saneamentoambiental/SensorUmidade/src/CustomHtmlFormatProvider.h

#ifndef _CustomHtmlFormatProvider_H_
#define _CustomHtmlFormatProvider_H_

#include <IotWebConf.h>

const char CUSTOMHTML_CSS_INNER[] PROGMEM = "\n\
.f{width:95% }\
.container { padding: 2px 16px; }\
.center{text-align:center!important}\
.card{box-shadow: 0 8px 16px 0 rgba(0,0,0,0.2);  padding: 0 8px;float: left;box-sizing: inherit; content: ""; display: table;}\
.lg{color:#000!important;background-color:#f1f1f1!important}\
.footer { position: fixed; left: 0; bottom: 0; width: 100%; background-color: aquamarine; color: black; text-align: center; };\
";

// -- Javascript block will be added to the header.
const char CUSTOMHTML_SCRIPT_INNER[] PROGMEM = "\n\
document.addEventListener('DOMContentLoaded', function(event) {\n\
  let elements = document.querySelectorAll('input[type=\"password\"]');\n\
  for (let p of elements) {\n\
  	let btn = document.createElement('INPUT'); btn.type = 'button'; btn.value = '🔓'; btn.style.width = 'auto'; p.style.width = '83%'; p.parentNode.insertBefore(btn,p.nextSibling);\n\
    btn.onclick = function() { if (p.type === 'password') { p.type = 'text'; btn.value = '🔒'; } else { p.type = 'password'; btn.value = '🔓'; } }\n\
  };\n\
});\n";
// -- HTML element will be added inside the body element.
const char CUSTOMHTML_BODY_INNER[] PROGMEM = "<div><img style='height: 200px;' src='data:image/png;base64, \
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\
'/></div>\n";
// -- This is an OOP technique to override behaviour of the existing
// IotWebConfHtmlFormatProvider. Here two method are overriden from
// the original class. See IotWebConf.h for all potentially overridable
// methods of IotWebConfHtmlFormatProvider .
class CustomHtmlFormatProvider : public IotWebConfHtmlFormatProvider
{
	
protected:
  String getScriptInner() override
  {
    return
      IotWebConfHtmlFormatProvider::getScriptInner() +
      String(FPSTR(CUSTOMHTML_SCRIPT_INNER));
  }
  String getStyleInner() override
  {
	  return
      IotWebConfHtmlFormatProvider::getStyleInner() +
      String(FPSTR(CUSTOMHTML_CSS_INNER));
  }
  String getBodyInner() override
  {
    return
      String(FPSTR(CUSTOMHTML_BODY_INNER)) +
      IotWebConfHtmlFormatProvider::getBodyInner();
  }
  
};

#endif //_CustomHtmlFormatProvider_H_
